SakshamBandlish/Smart-Switch-ESP32/SchematicESP32.kicad_sch

## KiCad design SchematicESP32.kicad_sch (2026-07-01, last stored version)

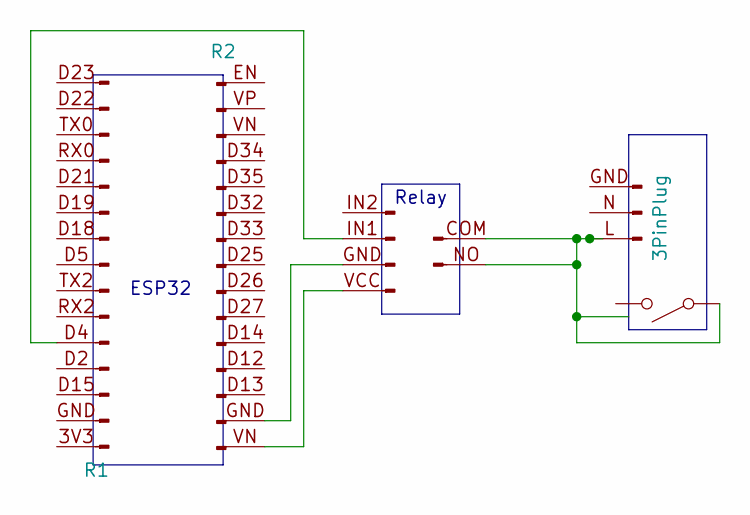
[picture p3: schematic SchematicESP32.kicad_sch]

Parts:
3PinPlug: (no value)
R, R1, R2: (no value)
Relay: (no value)
SW1: (no value)

Connections:
unnamed: 3PinPlug.L (Pin_1), R.COM (Pin_1), R.NO (Pin_2), SW1.
unnamed: R1.D4 (Pin_5), Relay.IN1 (Pin_3)
unnamed: R2.GND (Pin_14), Relay.GND (Pin_2)
unnamed: R2.VN (Pin_3), Relay.VCC (Pin_1)

Notes on the sheet:
Relay
ESP32
